jassar-robotics/prosthetic-hand-docs/cad/step files/l_wrist_interface.step

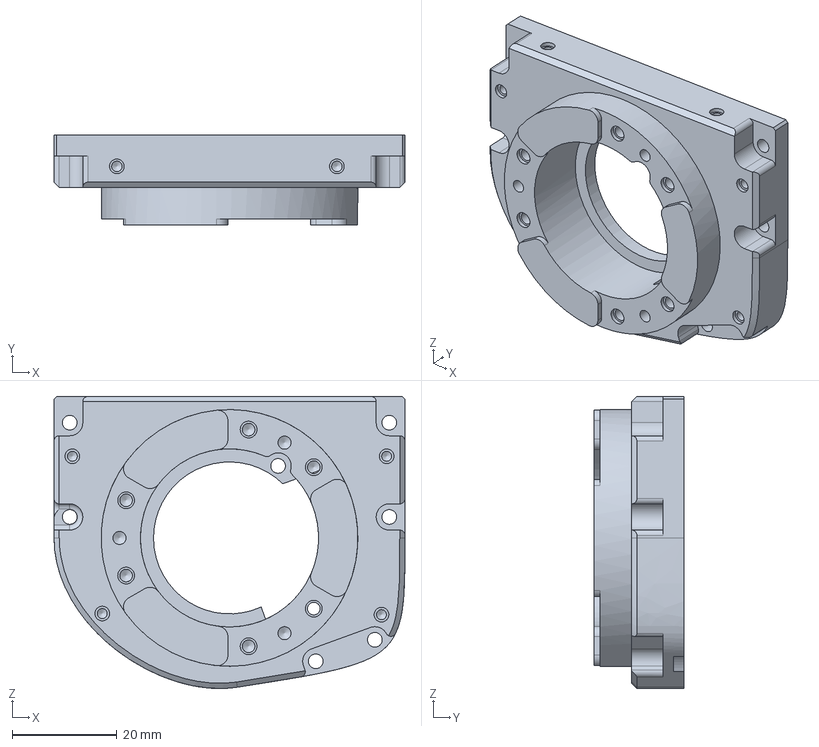
[picture p15: CAD file, 2025-12-29]
cad/step files/l_wrist_interface.step
67.0 x 17.2 x 55.7 mm
