jassar-robotics/prosthetic-hand-docs/cad/step files/u_ring_motor_mount.step

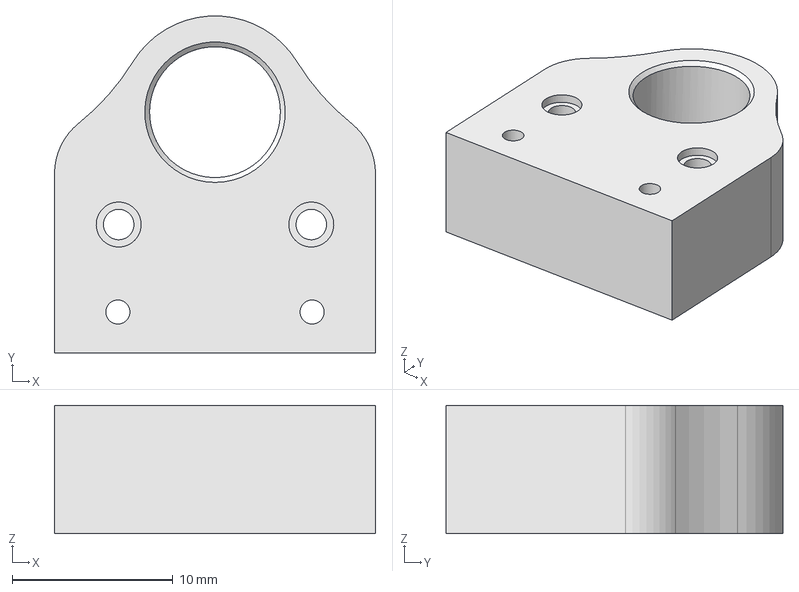
[picture p16: CAD file, 2025-12-29]
cad/step files/u_ring_motor_mount.step
20.0 x 21.0 x 8.00 mm
